bwasserm/sensaor/build.rs

fn main() {
    // Tell rustc to pass linker scripts to LLD
    // println!("cargo:rustc-link-arg=-Tmemory.x");
    // println!("cargo:rustc-link-arg=-Tlink.x");

    // Rerun this script only when necesary
    println!("cargo:rerun-if-changed=memory.x");
    println!("cargo:rerun-if-changed=build.rs");
}
